leeyumsk/IRL-Subtitles/Media/ESP32GlassV1.2.png

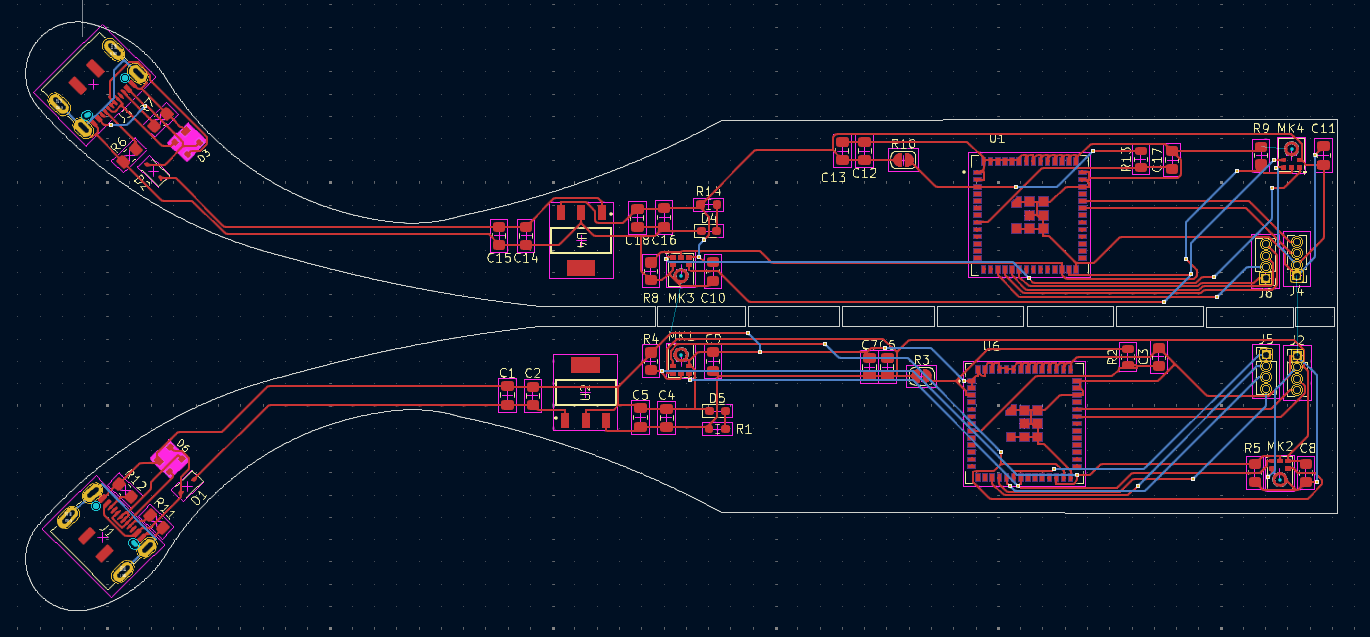
Media/ESP32GlassV1.2.png
